ybhvf/Defcon32-Badge/Hardware/3D/Bezel.SLDPRT

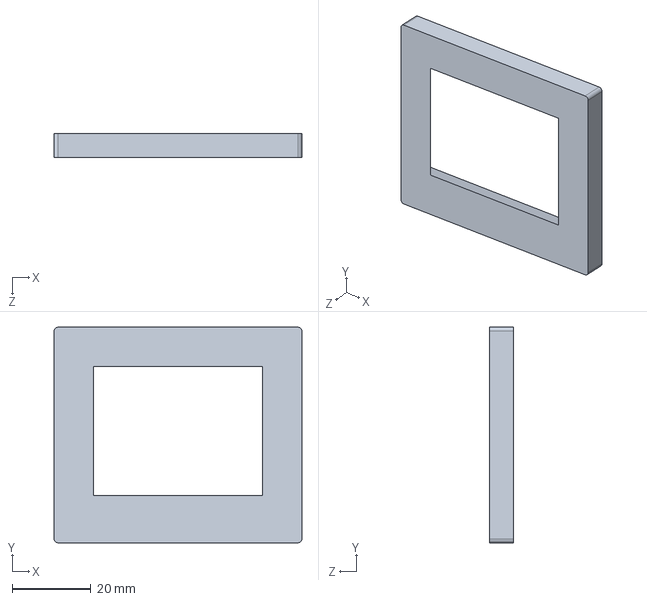
[picture p16: CAD file, 2024-06-11]
Hardware/3D/Bezel.SLDPRT
62.8 x 54.6 x 6.00 mm
