ybhvf/Defcon32-Badge/Hardware/3D/WS2812B-4020--3DModel-STEP-269445.STEP

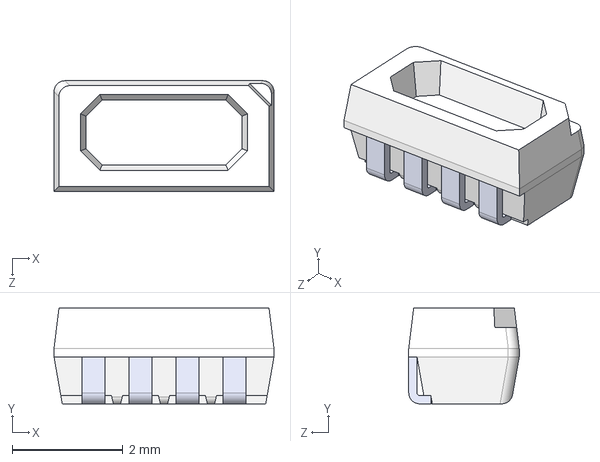
[picture p17: CAD file, 2024-06-11]
Hardware/3D/WS2812B-4020--3DModel-STEP-269445.STEP
3.98 x 1.73 x 2.00 mm
