ybhvf/Defcon32-Badge/Hardware/3D/3AAA Battery Box - Flying Leads.SLDPRT

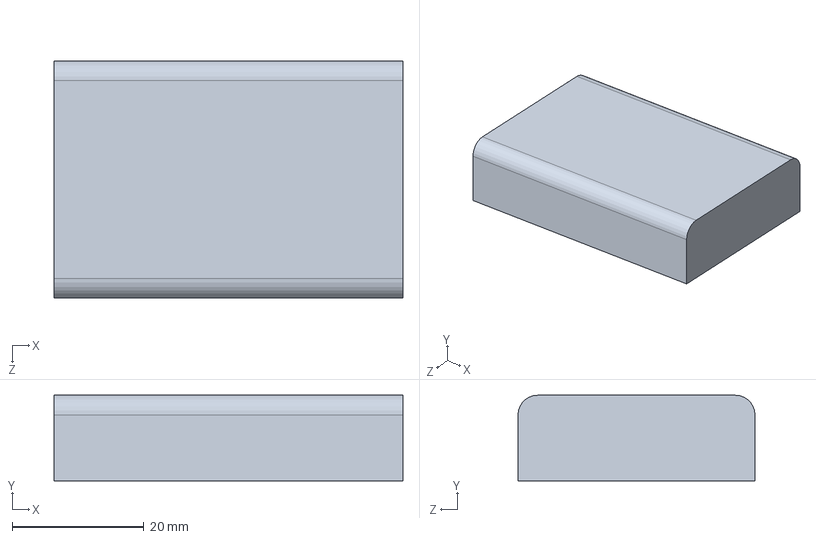
[picture p18: CAD file, 2024-05-20]
Hardware/3D/3AAA Battery Box - Flying Leads.SLDPRT
53.0 x 13.0 x 36.0 mm
