ybhvf/Defcon32-Badge/Hardware/3D/ER-TFT020-1-2476 Display.SLDPRT

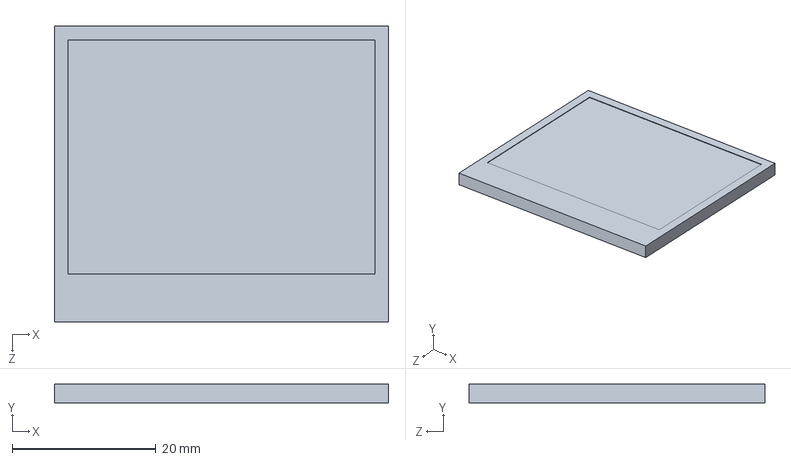
[picture p19: CAD file, 2024-05-20]
Hardware/3D/ER-TFT020-1-2476 Display.SLDPRT
46.5 x 2.62 x 41.2 mm
