ybhvf/Defcon32-Badge/Hardware/output/1.0/dc32.pdf

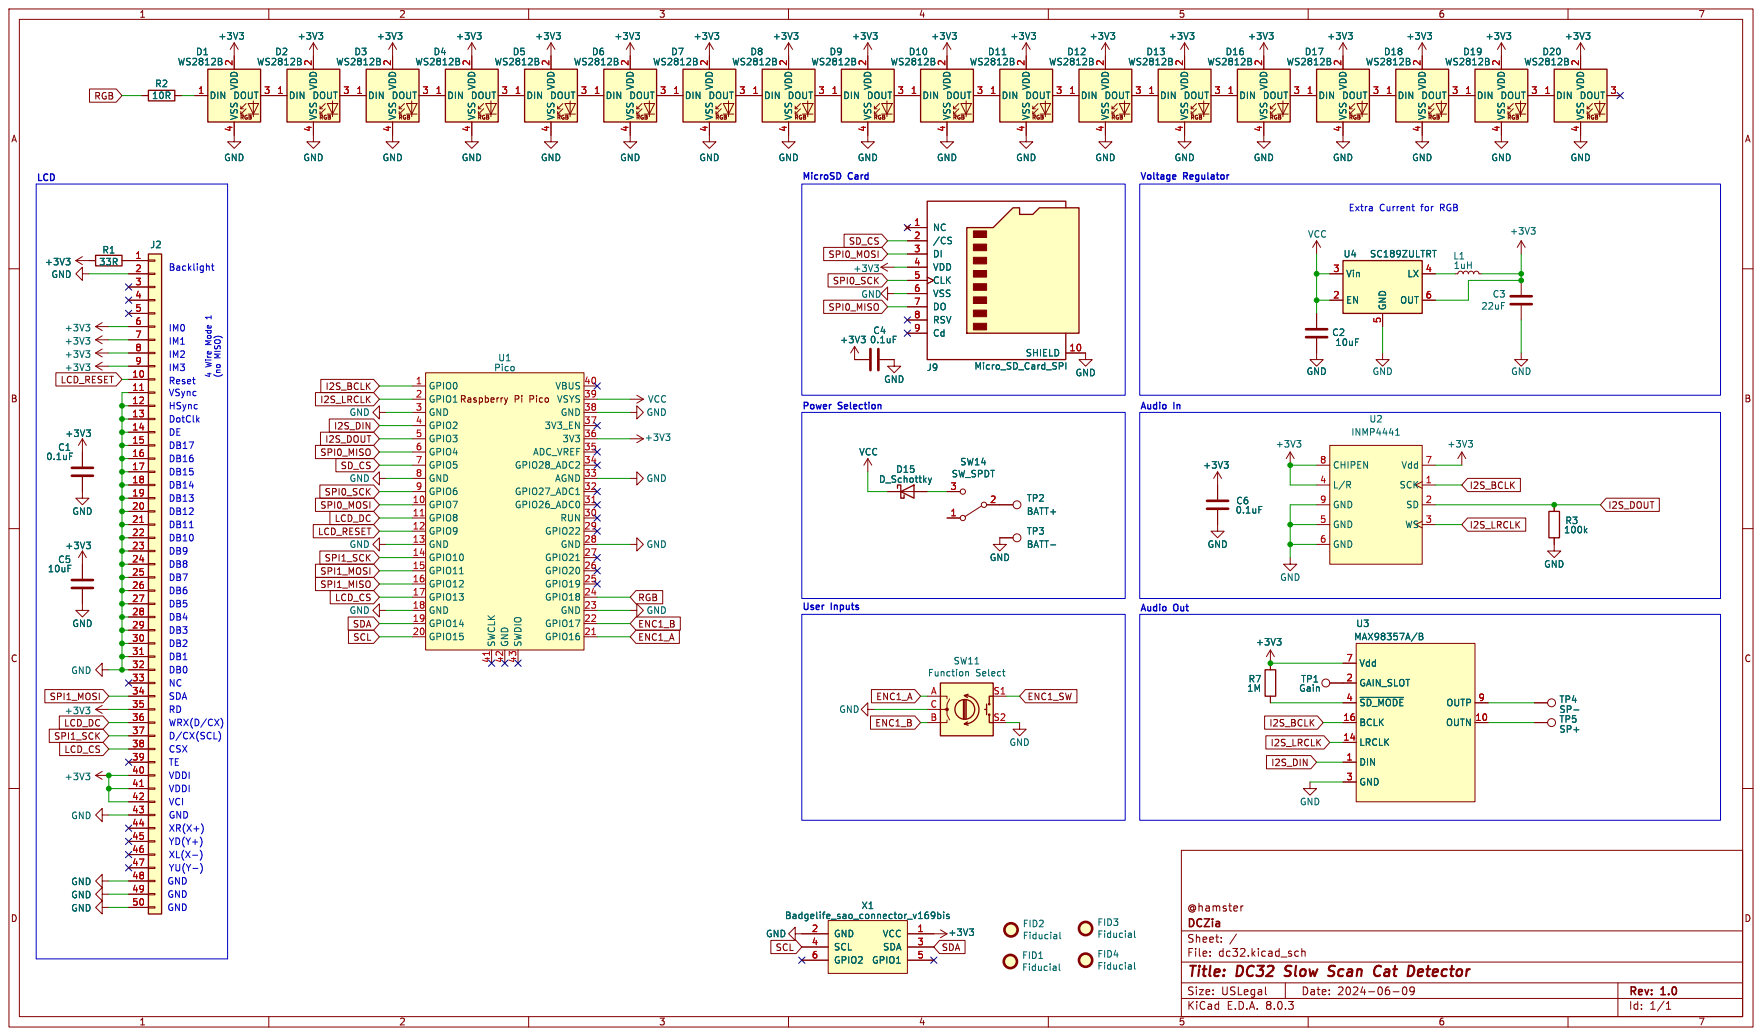
[picture p20: page 1]

Id: 1/1 Title: DC32 Slow Scan Cat Detector File: dc32.kicad_sch Sheet: / DCZia @hamster A
