ybhvf/Defcon32-Badge/Software/ziatv/playwav.py

# The MIT License (MIT)
# Copyright (c) 2022 Mike Teachman
# https://opensource.org/licenses/MIT

# Purpose:  Play a WAV audio file out of a speaker or headphones
#
# - read audio samples from a WAV file on SD Card
# - write audio samples to an I2S amplifier or DAC module
# - the WAV file will play continuously in a loop until
#   a keyboard interrupt is detected or the board is reset
#
# blocking version
# - the write() method blocks until the entire sample buffer is written to the I2S interface

import os
from machine import I2S
from machine import Pin

if os.uname().machine.count("Raspberry"):
    from lib.sdcard import SDCard
    from machine import SPI

    cs = Pin(5, machine.Pin.OUT)
    spi = SPI(
        0,
        baudrate=1_000_000,  # this has no effect on spi bus speed to SD Card
        polarity=0,
        phase=0,
        bits=8,
        firstbit=machine.SPI.MSB,
        sck=Pin(6),
        mosi=Pin(7),
        miso=Pin(4),
    )

    sd = SDCard(spi, cs)
    sd.init_spi(25_000_000)  # increase SPI bus speed to SD card
    os.mount(sd, "/sd")

    # ======= I2S CONFIGURATION =======
    SCK_PIN = 0
    WS_PIN = 1
    SD_PIN = 2
    I2S_ID = 0
    BUFFER_LENGTH_IN_BYTES = 40000
    # ======= I2S CONFIGURATION =======

elif os.uname().machine.count("MIMXRT"):
    from machine import SDCard

    sd = SDCard(1)  # Teensy 4.1: sck=45, mosi=43, miso=42, cs=44
    os.mount(sd, "/sd")

    # ======= I2S CONFIGURATION =======
    SCK_PIN = 4
    WS_PIN = 3
    SD_PIN = 2
    I2S_ID = 2
    BUFFER_LENGTH_IN_BYTES = 40000
    # ======= I2S CONFIGURATION =======

else:
    print("Warning: program not tested with this board")

# ======= AUDIO CONFIGURATION =======
WAV_FILE = "mic.wav" 
WAV_SAMPLE_SIZE_IN_BITS = 16
FORMAT = I2S.MONO
SAMPLE_RATE_IN_HZ = 44100
# ======= AUDIO CONFIGURATION =======

audio_out = I2S(
    I2S_ID,
    sck=Pin(SCK_PIN),
    ws=Pin(WS_PIN),
    sd=Pin(SD_PIN),
    mode=I2S.TX,
    bits=WAV_SAMPLE_SIZE_IN_BITS,
    format=FORMAT,
    rate=SAMPLE_RATE_IN_HZ,
    ibuf=BUFFER_LENGTH_IN_BYTES,
)

wav = open("/sd/{}".format(WAV_FILE), "rb")
_ = wav.seek(44)  # advance to first byte of Data section in WAV file

# allocate sample array
# memoryview used to reduce heap allocation
wav_samples = bytearray(10000)
wav_samples_mv = memoryview(wav_samples)

# continuously read audio samples from the WAV file
# and write them to an I2S DAC
print("==========  START PLAYBACK ==========")
try:
    while True:
        num_read = wav.readinto(wav_samples_mv)
        # end of WAV file?
        if num_read == 0:
            # end-of-file, advance to first byte of Data section
            _ = wav.seek(44)
        else:
            _ = audio_out.write(wav_samples_mv[:num_read])
except (KeyboardInterrupt, Exception) as e:
    print("caught exception {} {}".format(type(e).__name__, e))

# cleanup
wav.close()
os.umount("/sd")
spi.deinit()
audio_out.deinit()
print("Done")
